aws-samples/aws-iot-connected-product-demo-badge/pictures/raw/toy.jpg

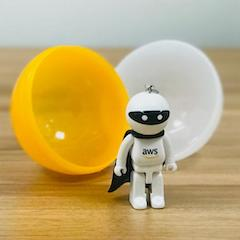
pictures/raw/toy.jpg
